alex1115alex/Wearables-Telescope/smartglass8bit/myfont12pt7b.h

const uint8_t myfont12pt7bBitmaps[] PROGMEM = {
  0x00, 0xFF, 0xFF, 0xFF, 0x49, 0x24, 0x07, 0xE0, 0xFF, 0xFF, 0xFF, 0xFD,
  0x20, 0x43, 0x03, 0x08, 0x18, 0x60, 0x43, 0x02, 0x18, 0x7F, 0xFC, 0xC2,
  0x02, 0x18, 0x10, 0xC0, 0x86, 0x04, 0x31, 0xFF, 0xF1, 0x86, 0x0C, 0x30,
  0x21, 0x81, 0x0C, 0x0C, 0x30, 0x04, 0x03, 0xE1, 0xF7, 0x32, 0x6E, 0x46,
  0x08, 0xC1, 0x18, 0x2E, 0x0F, 0xC7, 0xE1, 0xD0, 0x72, 0x0C, 0x41, 0x88,
  0xF1, 0x1B, 0x27, 0x7F, 0xC3, 0xE0, 0x10, 0x02, 0x00, 0x0C, 0x07, 0x03,
  0x03, 0x60, 0x61, 0x8C, 0x18, 0x63, 0x03, 0x18, 0xC0, 0xC6, 0x30, 0x19,
  0xDC, 0x06, 0x3E, 0x00, 0xC7, 0x1F, 0x30, 0x06, 0xE6, 0x03, 0x19, 0x80,
  0xC6, 0x30, 0x31, 0x8C, 0x0C, 0x61, 0x83, 0xB8, 0x60, 0x7C, 0x0C, 0x0E,
  0x01, 0x80, 0x03, 0xC0, 0x1F, 0x80, 0xE3, 0x03, 0x8C, 0x0E, 0x30, 0x1D,
  0x80, 0x7E, 0x00, 0x70, 0x03, 0xF1, 0x8C, 0xE7, 0x71, 0xCF, 0x83, 0x3C,
  0x0C, 0xE0, 0x37, 0xC1, 0xFB, 0xFE, 0x43, 0xF0, 0xFF, 0xFE, 0x80, 0xC1,
  0x86, 0x0C, 0x30, 0x61, 0x86, 0x18, 0x61, 0xC7, 0x18, 0x61, 0x86, 0x18,
  0xC3, 0x18, 0x63, 0x00, 0x0C, 0x63, 0x0C, 0x61, 0x86, 0x30, 0xC3, 0x0C,
  0x30, 0xC3, 0x0C, 0x18, 0x61, 0x83, 0x0C, 0x18, 0x30, 0x18, 0x18, 0xF6,
  0x7F, 0x38, 0x6C, 0x26, 0x07, 0x00, 0x38, 0x01, 0xC0, 0x0E, 0x00, 0x70,
  0x7F, 0xFF, 0xFF, 0xE0, 0xE0, 0x07, 0x00, 0x38, 0x01, 0xC0, 0xFB, 0x40,
  0xFF, 0xFC, 0xFC, 0xC1, 0x81, 0x03, 0x06, 0x04, 0x0C, 0x18, 0x30, 0x20,
  0x60, 0xC1, 0x81, 0x83, 0x06, 0x06, 0x1F, 0x07, 0xF1, 0xC7, 0x38, 0xEE,
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
  {   741,  11,  17,  15,    1,  -16 },   // 0x46 'F'
  {   765,  16,  17,  19,    1,  -16 },   // 0x47 'G'
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

const GFXfont myfont12pt7b PROGMEM = {
  (uint8_t  *)myfont12pt7bBitmaps,
  (GFXglyph *)myfont12pt7bGlyphs,
  0x20, 0x7E, 24 };

// Approx. 2644 bytes
