alex1115alex/Wearables-Telescope/smartglass8bit/myfont9pt7b.h

const uint8_t myfont9pt7bBitmaps[] PROGMEM = {
  0x00, 0x6D, 0xB6, 0xF6, 0xD8, 0x36, 0xDE, 0xF7, 0xBD, 0x80, 0x44, 0x22,
  0x11, 0x88, 0xCF, 0xF9, 0x10, 0x88, 0x46, 0xFF, 0xFF, 0xC4, 0x42, 0x21,
  0x18, 0x08, 0x3E, 0x6B, 0xC9, 0x09, 0x09, 0x0E, 0x3C, 0x68, 0xC8, 0xC9,
  0xC9, 0x6B, 0x7E, 0x08, 0x08, 0x10, 0x70, 0x21, 0x20, 0x8C, 0xC1, 0x33,
  0x04, 0xC8, 0x09, 0xE0, 0x23, 0x1E, 0x40, 0x99, 0x02, 0x62, 0x09, 0x8C,
  0x26, 0x10, 0x70, 0x60, 0x0F, 0x03, 0xF0, 0x66, 0x0C, 0xC0, 0xF0, 0x0E,
  0x01, 0xE3, 0x66, 0x78, 0x47, 0x0C, 0xC1, 0x7C, 0x64, 0xF8, 0xFF, 0xC0,
  0x84, 0x62, 0x23, 0x31, 0x11, 0x33, 0x32, 0x64, 0x80, 0x12, 0x24, 0x4C,
  0xCC, 0xCC, 0xCC, 0x44, 0x62, 0x10, 0x22, 0xAF, 0xCC, 0x59, 0x20, 0x18,
  0x18, 0x18, 0xFF, 0x18, 0x18, 0x18, 0x18, 0xFA, 0x40, 0xF8, 0xF0, 0x86,
  0x10, 0x86, 0x10, 0x84, 0x30, 0x84, 0x21, 0x80, 0x3C, 0x66, 0x42, 0xC3,
  0xC3, 0xC3, 0xC3, 0xC3, 0xC3, 0xC3, 0x42, 0x66, 0x3C, 0x86, 0x39, 0xFC,
  0xE3, 0x18, 0xC6, 0x31, 0x8C, 0x00, 0x3C, 0x7E, 0xC3, 0xC3, 0xC0, 0x40,
  0x60, 0x30, 0x18, 0x0C, 0x06, 0x03, 0xFF, 0x3C, 0x7E, 0x63, 0x43, 0x40,
  0x20, 0x78, 0xE0, 0xC0, 0xC2, 0xC3, 0x63, 0x3C, 0x20, 0x18, 0x0E, 0x05,
  0x02, 0xC1, 0x30, 0x88, 0x46, 0x21, 0xFF, 0xC8, 0x04, 0x02, 0x00, 0x7E,
  0x02, 0x02, 0x03, 0x3F, 0x63, 0xC0, 0xC0, 0xC0, 0xC3, 0x63, 0x3E, 0x3C,
  0x7E, 0xC7, 0x43, 0x01, 0x3D, 0x63, 0xC1, 0xC1, 0xC1, 0xC1, 0x62, 0x3C,
  0xFF, 0xC0, 0x60, 0x30, 0x30, 0x18, 0x18, 0x0C, 0x0C, 0x0C, 0x04, 0x04,
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
  {   415,   9,  13,  11,    1,  -12 },   // 0x46 'F'
  {   430,  12,  13,  14,    1,  -12 },   // 0x47 'G'
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

const GFXfont myfont9pt7b PROGMEM = {
  (uint8_t  *)myfont9pt7bBitmaps,
  (GFXglyph *)myfont9pt7bGlyphs,
  0x20, 0x7E, 18 };

// Approx. 1801 bytes
