alex1115alex/Wearables-Telescope/smartglass8bit/myfont4pt7b.h

const uint8_t myfont4pt7bBitmaps[] PROGMEM = {
  0x00, 0xFC, 0xF0, 0xAA, 0x76, 0xD5, 0x6D, 0x2C, 0xDE, 0x40, 0x4C, 0xD3,
  0x76, 0xD3, 0x20, 0x32, 0x89, 0x64, 0xF8, 0xC0, 0xA5, 0x5A, 0x6A, 0xA9,
  0x5F, 0x00, 0x21, 0x3E, 0x40, 0xC0, 0xC0, 0x80, 0xAA, 0x50, 0x69, 0x99,
  0x96, 0xBA, 0xA0, 0xE9, 0x84, 0x2F, 0x69, 0x8C, 0x9E, 0x44, 0xA9, 0xF8,
  0xE2, 0x2D, 0xAF, 0x69, 0x1F, 0x9E, 0xF8, 0x44, 0x22, 0xEA, 0xAF, 0x96,
  0x69, 0x9E, 0x8F, 0x90, 0x98, 0x86, 0x3C, 0xFF, 0x1E, 0xC3, 0xE9, 0x84,
  0x04, 0x38, 0x8A, 0xCD, 0x5A, 0x6F, 0xE0, 0xBE, 0x21, 0x94, 0xAA, 0xC4,
  0x79, 0x9F, 0x9F, 0x74, 0x42, 0x18, 0xB8, 0x7C, 0x63, 0x18, 0xBC, 0xF1,
  0x1F, 0x1F, 0xF1, 0x1F, 0x11, 0x74, 0xC3, 0x98, 0xB8, 0x99, 0x9F, 0x99,
  0xFC, 0x92, 0x4B, 0xC0, 0xCA, 0x4A, 0x74, 0xC4, 0x11, 0x11, 0x1F, 0xDE,
  0xF7, 0x7A, 0xD4, 0x99, 0xBD, 0xD9, 0x74, 0x63, 0x18, 0xB8, 0xF9, 0x97,
  0x11, 0x74, 0x63, 0x1A, 0xF8, 0x7C, 0x62, 0xF4, 0xC4, 0x79, 0x1E, 0x97,
  0xF2, 0x22, 0x22, 0x99, 0x99, 0x96, 0x8C, 0x64, 0xA2, 0x10, 0x93, 0x26,
  0x6B, 0x66, 0xC5, 0x80, 0x8A, 0x98, 0x47, 0x6C, 0x8A, 0x9C, 0x42, 0x10,
  0xF8, 0x42, 0x1F, 0xD5, 0x57, 0xAB, 0x50, 0xEA, 0xAB, 0x56, 0x80, 0xF8,
  0x80, 0xE9, 0xFF, 0x11, 0x79, 0x97, 0xE2, 0x3E, 0x88, 0xEA, 0xBE, 0xE9,
  0x7E, 0x9D, 0x50, 0xE9, 0xAC, 0xAE, 0x27, 0xDB, 0x40, 0xBC, 0x8A, 0xAB,
  0x27, 0x97, 0x40, 0xFC, 0xDE, 0x9A, 0x69, 0xF6, 0xD0, 0x69, 0x96, 0x79,
  0x9F, 0x11, 0xEA, 0xBE, 0x88, 0xD5, 0xE7, 0x70, 0xBA, 0x80, 0xB6, 0xF0,
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
  {    98,   4,   6,   5,    0,   -5 },   // 0x46 'F'
  {   101,   5,   6,   6,    0,   -5 },   // 0x47 'G'
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

const GFXfont myfont4pt7b PROGMEM = {
  (uint8_t  *)myfont4pt7bBitmaps,
  (GFXglyph *)myfont4pt7bGlyphs,
  0x20, 0x7E, 8 };

// Approx. 924 bytes
