alex1115alex/Wearables-Telescope/smartglass8bit/myfont6pt7b.h

const uint8_t myfont6pt7bBitmaps[] PROGMEM = {
  0x00, 0xFF, 0xB6, 0x80, 0x92, 0x49, 0x3F, 0x49, 0x2F, 0xCA, 0x24, 0x23,
  0xEA, 0x8A, 0x7A, 0x8A, 0xAB, 0x78, 0x80, 0x23, 0x11, 0x45, 0xA2, 0x50,
  0xB7, 0x42, 0xD1, 0x68, 0xE2, 0x00, 0x18, 0x68, 0xD0, 0xC1, 0xCA, 0xD8,
  0xB1, 0x9C, 0xE0, 0x99, 0x32, 0x49, 0x4A, 0x00, 0x4D, 0x49, 0x24, 0x89,
  0x80, 0xD6, 0xE0, 0x21, 0x3F, 0xF2, 0x10, 0xE0, 0xE0, 0x80, 0x93, 0x24,
  0x89, 0x20, 0x74, 0xE3, 0x18, 0xC7, 0x6E, 0x9A, 0xC9, 0x24, 0x7A, 0x28,
  0x30, 0x60, 0x40, 0xBF, 0x7A, 0x2C, 0x18, 0x82, 0x0C, 0xDE, 0x41, 0x85,
  0x12, 0x4B, 0xF4, 0x10, 0xF8, 0x20, 0x9E, 0x82, 0x08, 0xDE, 0x72, 0x27,
  0xBD, 0x8E, 0x28, 0x9C, 0xFA, 0x18, 0x43, 0x08, 0x42, 0x72, 0x28, 0x9C,
  0x8E, 0x18, 0x5E, 0xFA, 0x28, 0xFE, 0xFA, 0x04, 0x9E, 0xCC, 0x8F, 0x81,
  0x81, 0xC7, 0x62, 0x00, 0xFF, 0xFF, 0xFF, 0x0C, 0xEC, 0x30, 0x38, 0x30,
  0x76, 0x63, 0x04, 0x10, 0x80, 0x20, 0x1F, 0x0C, 0x31, 0x01, 0x4F, 0x29,
  0x13, 0x23, 0x54, 0x2A, 0x4D, 0x3F, 0x58, 0x10, 0xFC, 0x00, 0x18, 0x18,
  0x24, 0x24, 0x24, 0x5A, 0x42, 0x81, 0x7F, 0x1C, 0x51, 0xBE, 0x18, 0x5F,
  0x38, 0xDF, 0x08, 0x10, 0x20, 0x60, 0xA3, 0x3C, 0x3E, 0x86, 0x0C, 0x18,
  0x30, 0x50, 0x9F, 0xFC, 0x10, 0x41, 0x7C, 0x10, 0x7F, 0xFC, 0x10, 0x41,
  0x7C, 0x10, 0x41, 0x3C, 0x42, 0x82, 0x01, 0xF1, 0xF1, 0x82, 0x82, 0x7C,
  0x83, 0x06, 0x0F, 0xFF, 0xF0, 0x60, 0xC1, 0xFF, 0x84, 0x21, 0x08, 0x4A,
  0x6E, 0xC2, 0x44, 0x48, 0xF1, 0x64, 0x58, 0xE1, 0x08, 0x42, 0x10, 0x84,
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
  {   189,   6,   8,   7,    1,   -7 },   // 0x46 'F'
  {   195,   8,   9,   9,    0,   -8 },   // 0x47 'G'
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

const GFXfont myfont6pt7b PROGMEM = {
  (uint8_t  *)myfont6pt7bBitmaps,
  (GFXglyph *)myfont6pt7bGlyphs,
  0x20, 0x7E, 12 };

// Approx. 1159 bytes
